jan1s/hw-stm32-nixieclock/layout/control/c200.png

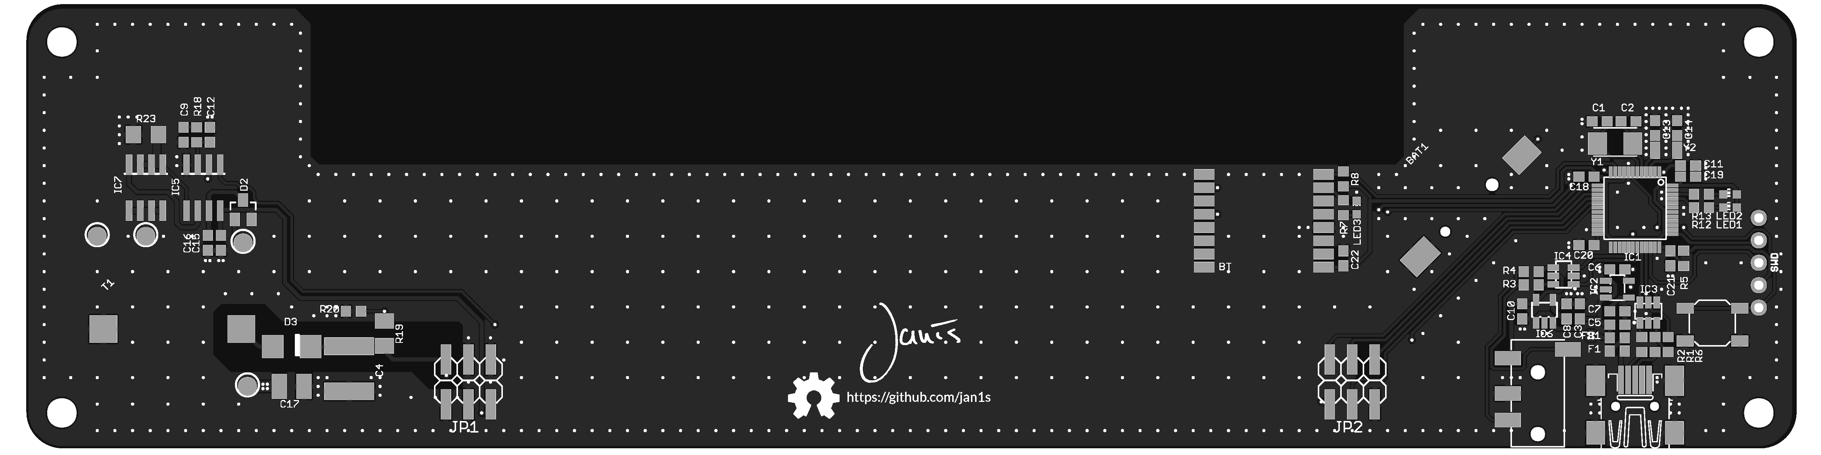
layout/control/c200.png
