jan1s/hw-stm32-nixieclock/layout/source/source_bt_rev_a.brd

## EAGLE design layout/source/source_bt_rev_a.brd (2016-01-02)

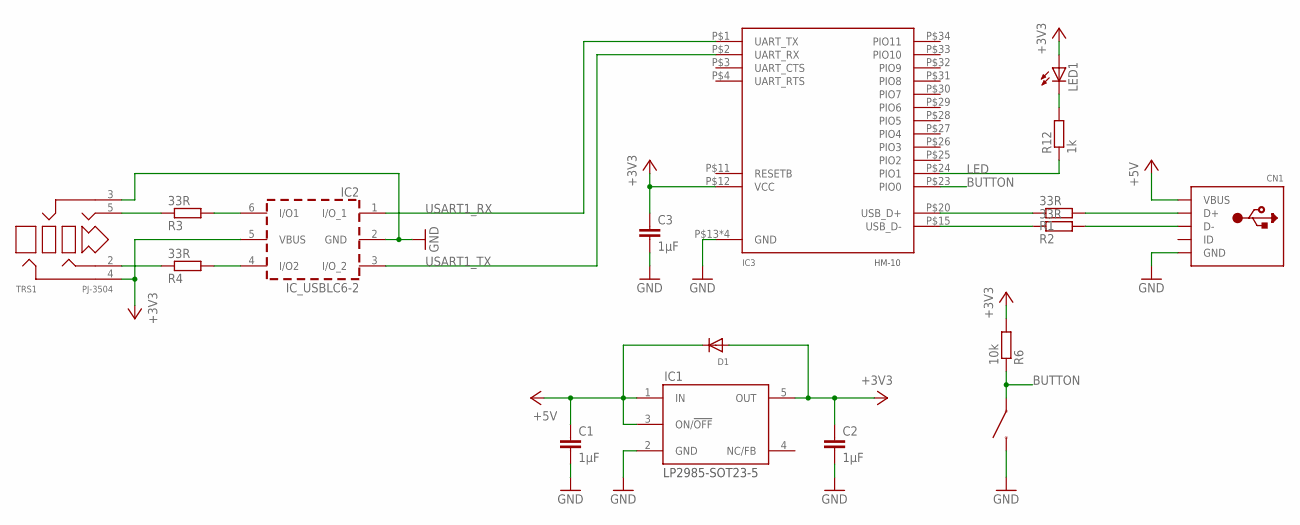
[picture p43: schematic source_bt_rev_a.sch, Microcontroller]

Parts:
C1, C2, C3: 1µF; C0603
CN1: USBMINIB; USB-MINIB
D1: DIODESOD-323; SOD-323
IC1: LP2985-SOT23-5; SOT23-5
IC2: IC_USBLC6-2; SOT-23-6L
IC3: HM-10
ISP: TACT-SWITCH-40-40; 40-40
LED1: LEDCHIP-LED0603; CHIP-LED0603
R1, R2, R3, R4: 33R; R0603
R6: 10k; R0603
R12: 1k; R0603
TRS1: PJ-3504; YD-PJ-3504

Connections:
+3V3: C2.1, C3.1, D1.A, IC1.5 (OUT), IC2.5 (VBUS), IC3.P$12 (VCC), LED1.A, R6.2, TRS1.4
+5V: C1.1, CN1.VBUS, D1.C, IC1.1 (IN), IC1.3 (ON/!OFF)
BUTTON: IC3.P$23 (PIO0), ISP.3, ISP.4, R6.1
GND: C1.2, C2.2, C3.2, CN1.GND, IC1.2 (GND), IC2.2 (GND), IC3.P$13 (GND), IC3.P$14 (GND), IC3.P$21 (GND), IC3.P$22 (GND), ISP.1, ISP.2, TRS1.3
LED: IC3.P$24 (PIO1), R12.1
unnamed: IC3.P$20 (USB_D+), R1.1
unnamed: IC3.P$15 (USB_D-), R2.1
unnamed: CN1.D+, R1.2
unnamed: CN1.D-, R2.2
unnamed: IC2.6 (I/O1), R3.2
unnamed: LED1.C, R12.2
unnamed: R4.1, TRS1.2
unnamed: IC2.4 (I/O2), R4.2
unnamed: R3.1, TRS1.5
USART1_RX: IC2.1 (I/O_1), IC3.P$1 (UART_TX)
USART1_TX: IC2.3 (I/O_2), IC3.P$2 (UART_RX)

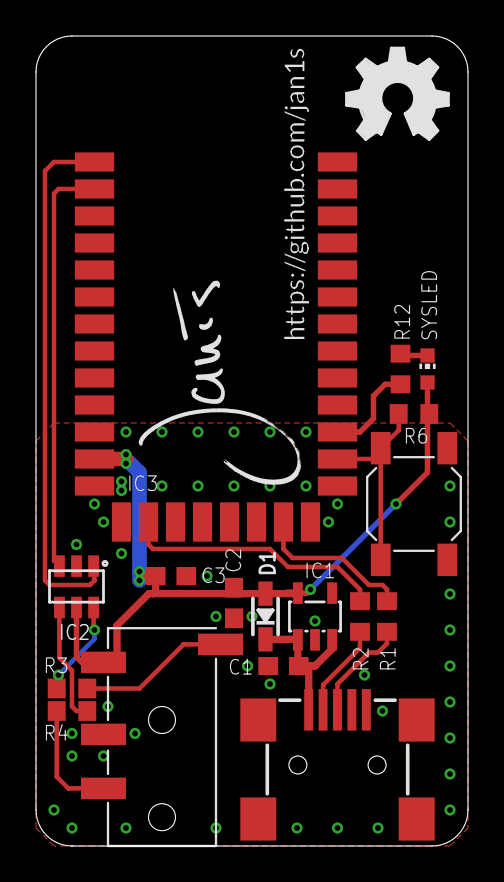
[picture p44: board source_bt_rev_a.brd from above]

Board: 2 copper layers, 24.0 x 45.0 mm, 22 parts (2 on the bottom side), 16 nets.

Other parts of the board:
LOGO1: OSHW_LOGO_FILLX0200-NT; OSHW_FILLX200_NOTEXT
U$1, U$2: JANIS_10MM
U$5, U$6: GITHUB/JAN1S
