jan1s/hw-stm32-nixieclock/production/c200_rev_b/c200_rev_b.sch

## EAGLE design production/c200_rev_b/c200_rev_b.sch (2017-11-01)

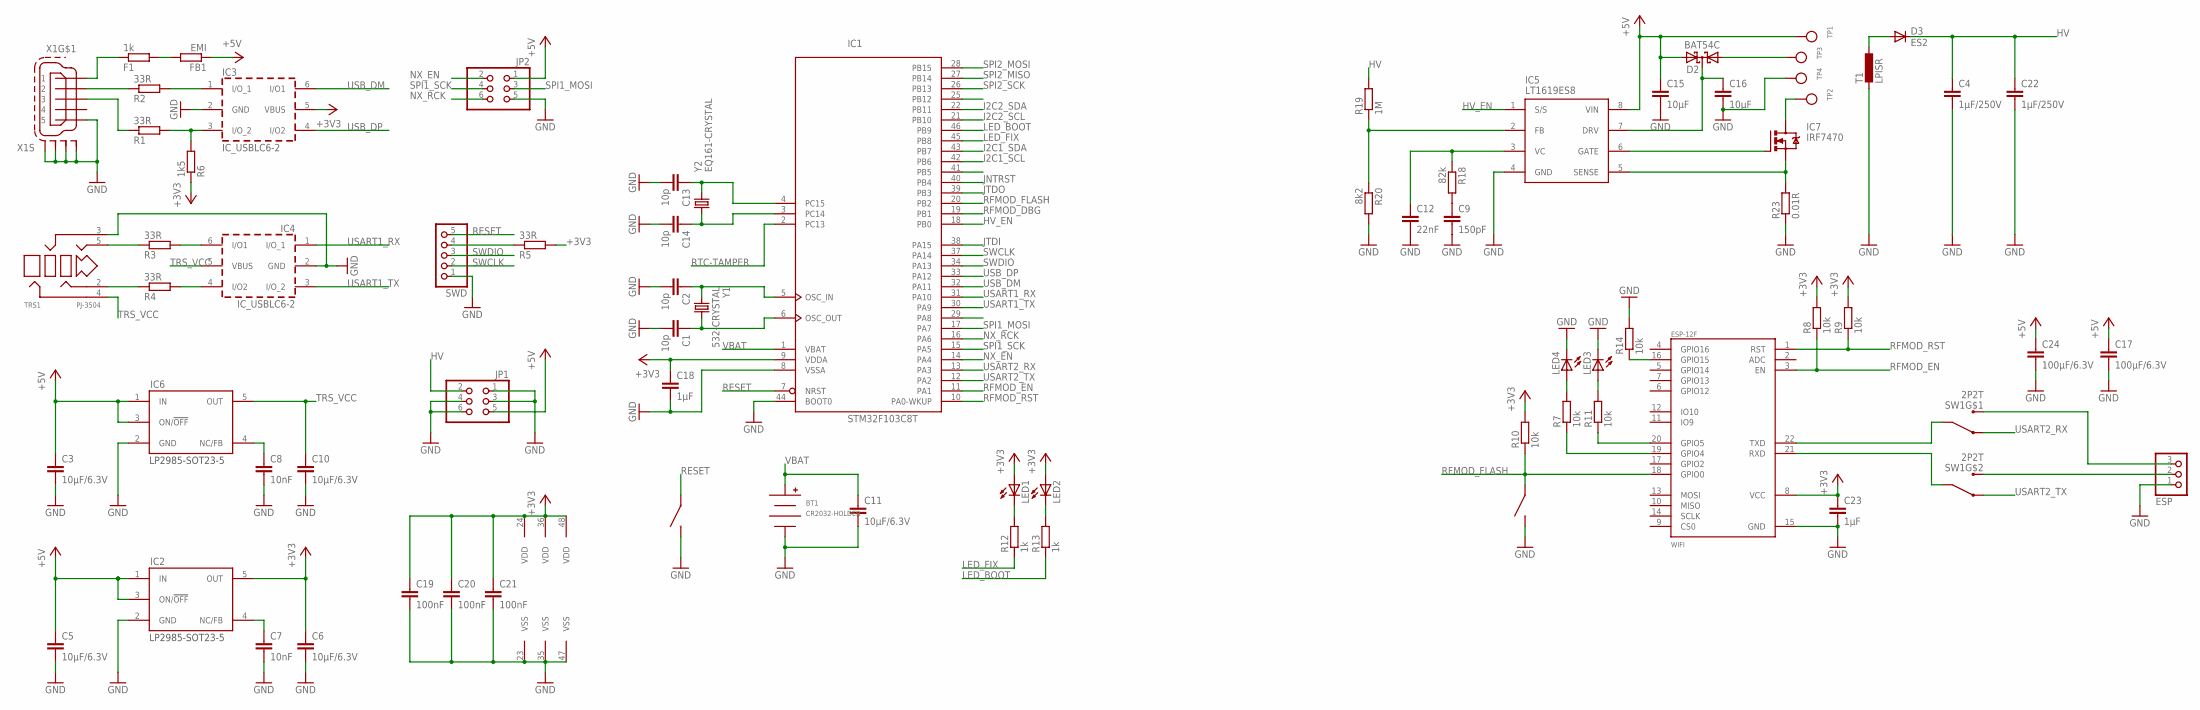
[picture p45: schematic c200_rev_b.sch]

Parts:
BT1: CR2032-HOLDER; CH28-2032LF
C1, C2, C13, C14: 10p; C0603
C3, C5, C6, C10, C11: 10µF/6.3V; C0603
C4, C22: 1µF/250V; C2220K
C7, C8: 10nF; C0603
C9: 150pF; C0603
C12: 22nF; C0603
C15, C16: 10µF; C0603
C17, C24: 100µF/6.3V; C1210
C18, C23: 1µF; C0603
C19, C20, C21: 100nF; C0603
D2: BAT54C; SOT23
D3: ES2; DO-214AA
ESP: HEADER-1X3ROUND; 1X03_ROUND
F1: 1k; R0603
FB1: EMI; R0603
FLASH: TACT-SWITCH-40-40; 40-40
IC1: STM32F103C8T; LQFP48
IC2, IC6: LP2985-SOT23-5; SOT23-5
IC3, IC4: IC_USBLC6-2; SOT-23-6L
IC5: LT1619ES8; SO8
IC7: IRF7470; SO8
ISP: TACT-SWITCH-40-40; 40-40
JP1, JP2: PINHD-2X3_2.54-SMD; 2X03SMD
LED1, LED2, LED3, LED4: LEDCHIP-LED0603; CHIP-LED0603
R1, R2, R3, R4, R5: 33R; R0603
R6: 1k5; R0603
R7, R8, R9, R10, R11, R14: 10k; R0603
R12, R13: 1k; R0603
R18: 82k; R0603
R19: 1M; M1206
R20: 8k2; R0603
R23: 0.01R; R1206
SW1: 2P2T; MSS22D18
SWD: HEADER-1X5ROUND; 1X05_ROUND
T1: LPISR; PISR
TP1, TP2, TP3, TP4: TESTPOINTROUND2MM; TESTPOINT_ROUND_2MM
TRS1: PJ-3504; YD-PJ-3504
WIFI: ESP-12F
X1: MINI-USB-SCHIELD-32005-201; 32005-201
Y1: 532-CRYSTAL; 2PIN50X32
Y2: EQ161-CRYSTAL; EQ161

Connections:
+3V3: C6.1, C18.1, C19.1, C20.1, C21.1, C23.1, IC1.9 (VDDA), IC1.24 (VDD), IC1.36 (VDD), IC1.48 (VDD), IC2.5 (OUT), IC3.5 (VBUS), LED1.A, LED2.A, R5.2, R6.1, R8.2, R9.2, R10.2, WIFI.8 (VCC)
+5V: C3.1, C5.1, C15.1, C17.1, C24.1, D2.2 (A2), FB1.1, IC2.1 (IN), IC2.3 (ON/!OFF), IC5.8 (VIN), IC6.1 (IN), IC6.3 (ON/!OFF), JP1.5, JP2.1, TP1.P$1
ASDAWJIODJA: R5.1, SWD.4
GND: BT1.NEG, C1.2, C2.2, C3.2, C4.2, C5.2, C6.2, C7.2, C8.2, C9.2, C10.2, C11.2, C12.2, C13.2, C14.2, C15.2, C16.2, C17.2, C18.2, C19.2, C20.2, C21.2, C22.2, C23.2, C24.2, ESP.1, FLASH.1, IC1.8 (VSSA), IC1.23 (VSS), IC1.35 (VSS), IC1.44 (BOOT0), IC1.47 (VSS), IC2.2 (GND), IC3.2 (GND), IC4.2 (GND), IC5.4 (GND), IC6.2 (GND), ISP.1, JP1.1, JP1.3, JP1.4, JP1.6, JP2.5, LED3.C, LED4.C, R14.2, R20.2, R23.1, SWD.1, T1.P$2 (2), TP4.P$1, TRS1.3, WIFI.15 (GND), X1.5, X1.M1 (S1), X1.M2 (S2), X1.M3 (S3), X1.M4 (S4)
HV: C4.1, C22.1, D3.C, JP1.2, R19.2
HV_EN: IC1.18 (PB0), IC5.1 (S/S)
I2C1_SCL: IC1.42 (PB6)
I2C1_SDA: IC1.43 (PB7)
I2C2_SCL: IC1.21 (PB10)
I2C2_SDA: IC1.22 (PB11)
JNTRST: IC1.40 (PB4)
JTDI: IC1.38 (PA15)
JTDO: IC1.39 (PB3)
LED_BOOT: IC1.46 (PB9), R13.1
LED_FIX: IC1.45 (PB8), R12.1
unnamed: C1.1, IC1.6 (OSC_OUT), Y1.P$1 (1)
unnamed: C2.1, IC1.5 (OSC_IN), Y1.P$2 (2)
unnamed: F1.1, X1.1
unnamed: C8.1, IC6.4 (NC/FB)
unnamed: IC3.3 (I/O_2), R1.2, R6.2
unnamed: R14.1, WIFI.16 (GPIO15)
unnamed: IC4.6 (I/O1), R3.2
unnamed: D2.1 (A1), TP3.P$1
unnamed: IC5.6 (GATE), IC7.4 (G)
unnamed: LED2.C, R13.2
unnamed: LED1.C, R12.2
unnamed: R4.1, TRS1.2
unnamed: IC7.5 (D), TP2.P$1
unnamed: C12.1, IC5.3 (VC), R18.1
unnamed: C9.1, R18.2
unnamed: D3.A, T1.P$1 (1)
unnamed: IC5.2 (FB), R19.1, R20.1
unnamed: IC5.5 (SENSE), IC7.1 (S), R23.2
unnamed: C16.1, D2.3 (CC), IC5.7 (DRV)
unnamed: C7.1, IC2.4 (NC/FB)
unnamed: SW1.C1 (C), WIFI.22 (TXD)
unnamed: F1.2, FB1.2
unnamed: IC3.1 (I/O_1), R2.2
unnamed: R2.1, X1.2
unnamed: IC4.4 (I/O2), R4.2
unnamed: SW1.C2 (C), WIFI.21 (RXD)
unnamed: R11.1, WIFI.20 (GPIO5)
unnamed: R3.1, TRS1.5
unnamed: C13.1, IC1.4 (PC15), Y2.P$1 (1)
unnamed: C14.1, IC1.3 (PC14), Y2.P$2 (2)
unnamed: ESP.3, SW1.B1 (B)
unnamed: ESP.2, SW1.B2 (B)
unnamed: R7.1, WIFI.19 (GPIO4)
unnamed: LED4.A, R7.2
unnamed: LED3.A, R11.2
unnamed: R1.1, X1.3
NX_EN: IC1.14 (PA4), JP2.2
NX_RCK: IC1.16 (PA6), JP2.6
RESET: IC1.7 (NRST), ISP.3, SWD.5
RFMOD_DBG: IC1.19 (PB1)
RFMOD_EN: IC1.11 (PA1), R8.1, WIFI.3 (EN)
RFMOD_FLASH: FLASH.3, IC1.20 (PB2), R10.1, WIFI.18 (GPIO0)
RFMOD_RST: IC1.10 (PA0-WKUP), R9.1, WIFI.1 (RST)
RTC-TAMPER: IC1.2 (PC13)
SPI1_MOSI: IC1.17 (PA7), JP2.3
SPI1_SCK: IC1.15 (PA5), JP2.4
SPI2_MISO: IC1.27 (PB14)
SPI2_MOSI: IC1.28 (PB15)
SPI2_SCK: IC1.26 (PB13)
SWCLK: IC1.37 (PA14), SWD.2
SWDIO: IC1.34 (PA13), SWD.3
TRS_VCC: C10.1, IC4.5 (VBUS), IC6.5 (OUT), TRS1.4
USART1_RX: IC1.31 (PA10), IC4.1 (I/O_1)
USART1_TX: IC1.30 (PA9), IC4.3 (I/O_2)
USART2_RX: IC1.13 (PA3), SW1.A1 (A)
USART2_TX: IC1.12 (PA2), SW1.A2 (A)
USB_DM: IC1.32 (PA11), IC3.6 (I/O1)
USB_DP: IC1.33 (PA12), IC3.4 (I/O2)
VBAT: BT1.POS, C11.1, IC1.1 (VBAT)
